kbob/filabilly-humidor/Fan and Surround/Dummy Fan/IMG_1981.jpeg

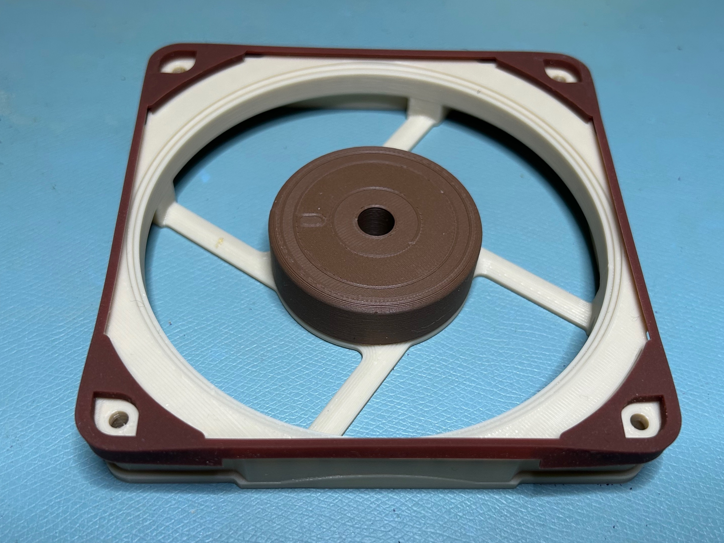
Fan and Surround/Dummy Fan/IMG_1981.jpeg
