kbob/filabilly-humidor/Fan and Surround/Dummy Fan/IMG_1982.jpeg

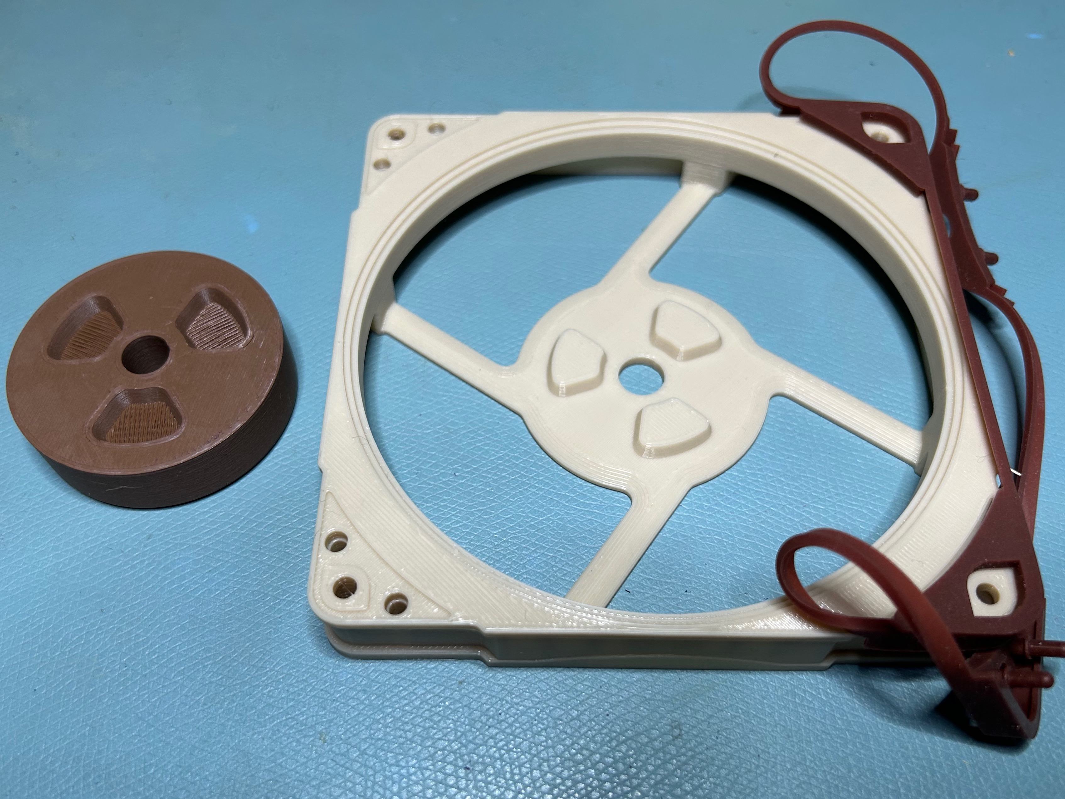
Fan and Surround/Dummy Fan/IMG_1982.jpeg
