kbob/filabilly-humidor/Fan and Surround/Dummy Fan/IMG_1983.jpeg

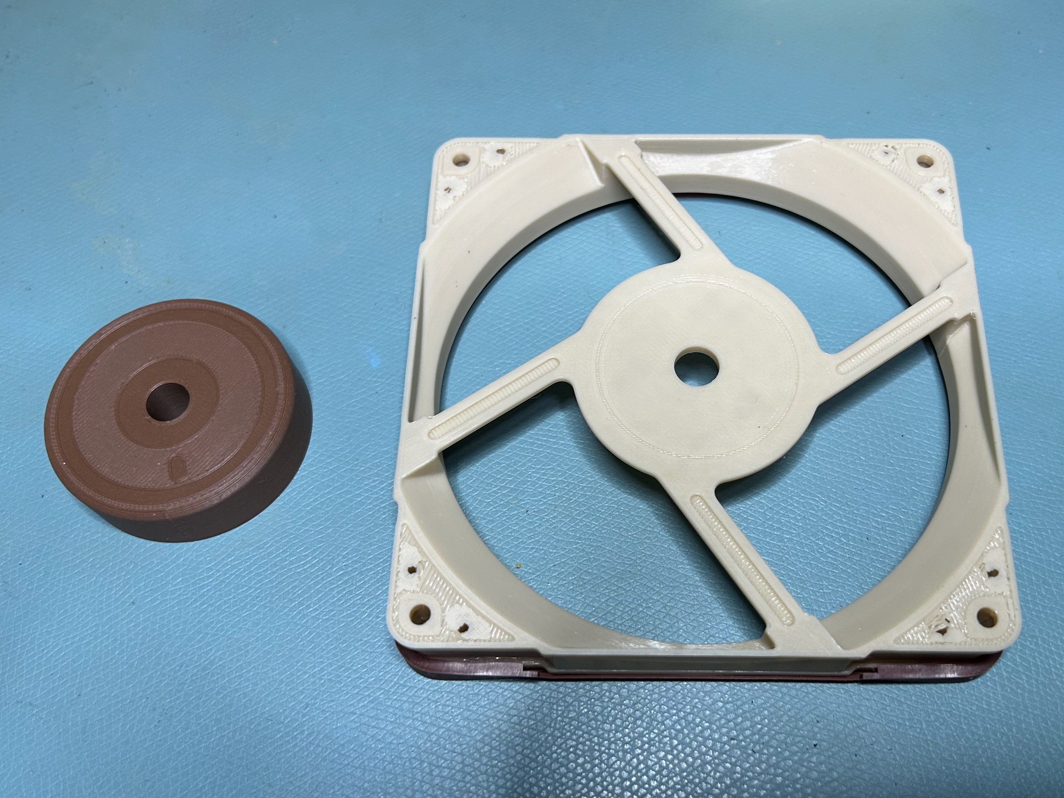
Fan and Surround/Dummy Fan/IMG_1983.jpeg
