kbob/filabilly-humidor/Fan and Surround/Fan Surround/IMG_1965.jpeg

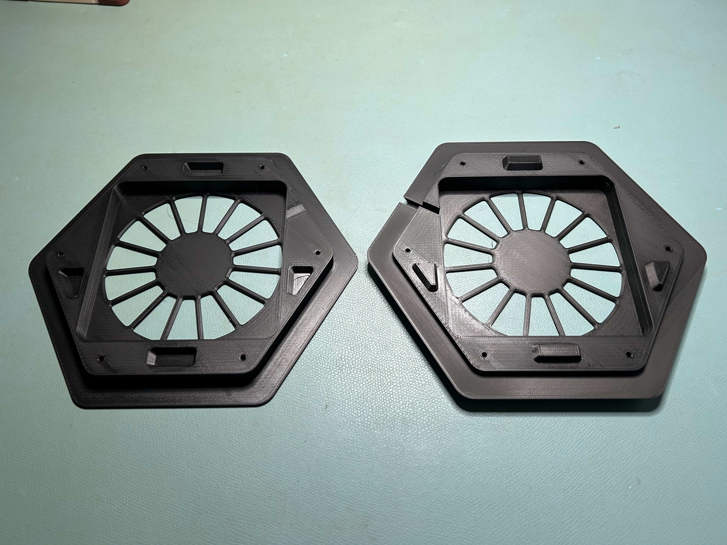
Fan and Surround/Fan Surround/IMG_1965.jpeg
