kbob/filabilly-humidor/Fan and Surround/Fan Surround/IMG_1976.jpeg

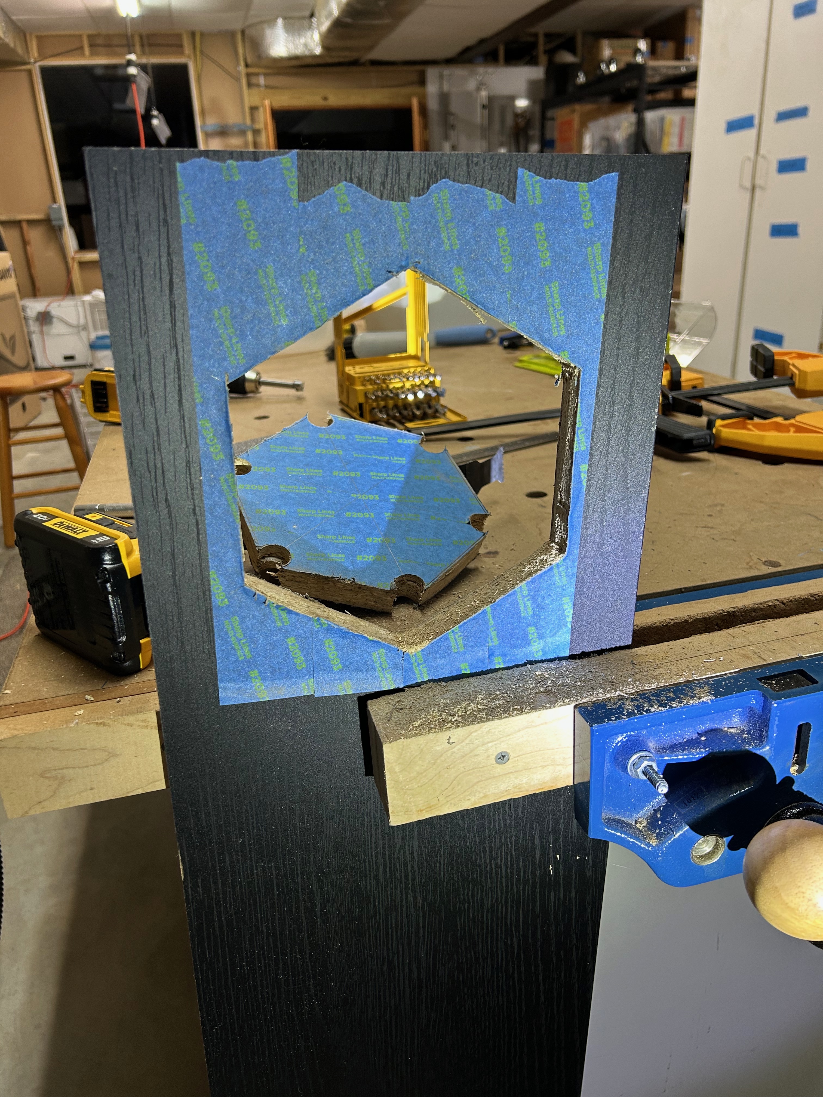
Fan and Surround/Fan Surround/IMG_1976.jpeg
