kbob/filabilly-humidor/Fan and Surround/Fan Surround/IMG_1977.jpeg

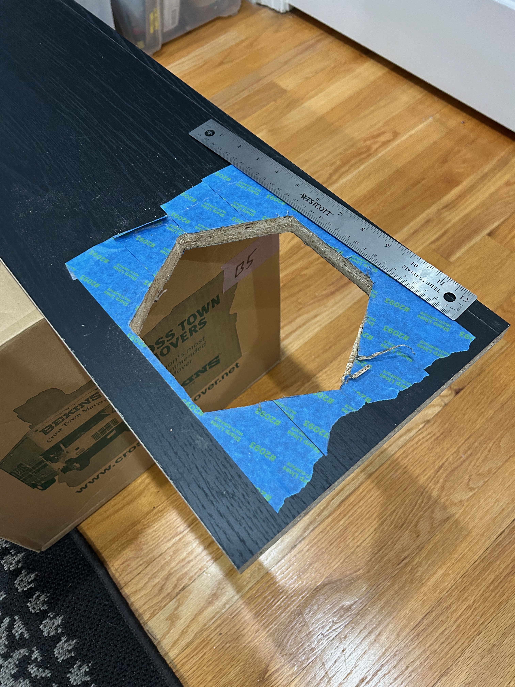
Fan and Surround/Fan Surround/IMG_1977.jpeg
