kbob/filabilly-humidor/Fan and Surround/Fan Surround/IMG_1978.jpeg

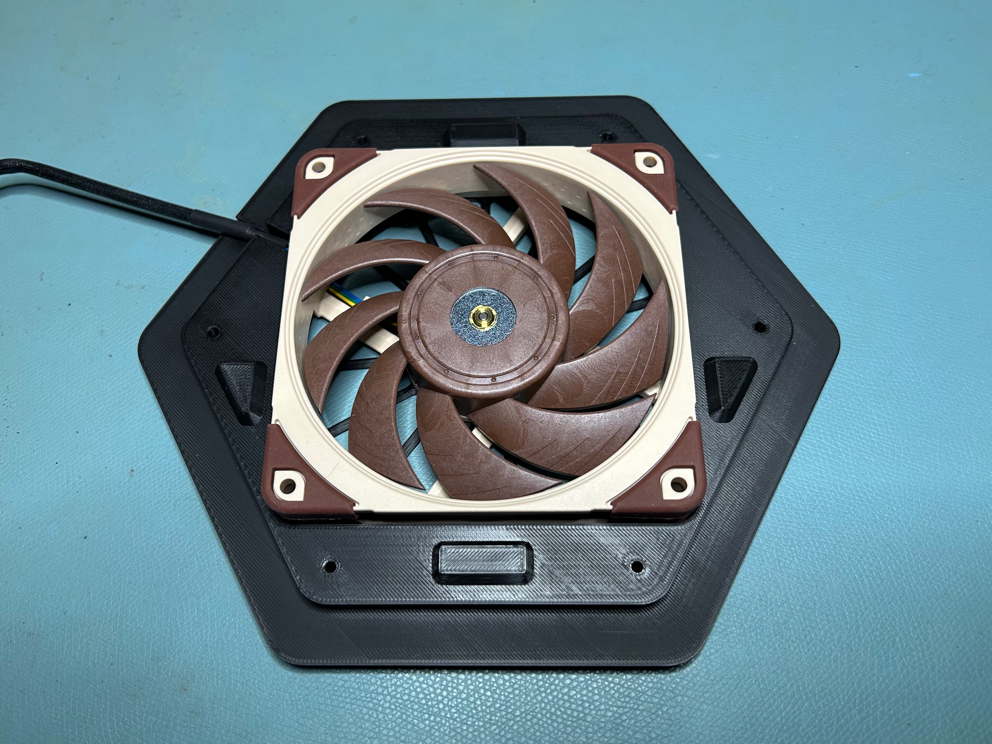
Fan and Surround/Fan Surround/IMG_1978.jpeg
