kbob/filabilly-humidor/Fan and Surround/Fan Surround/IMG_1979.jpeg

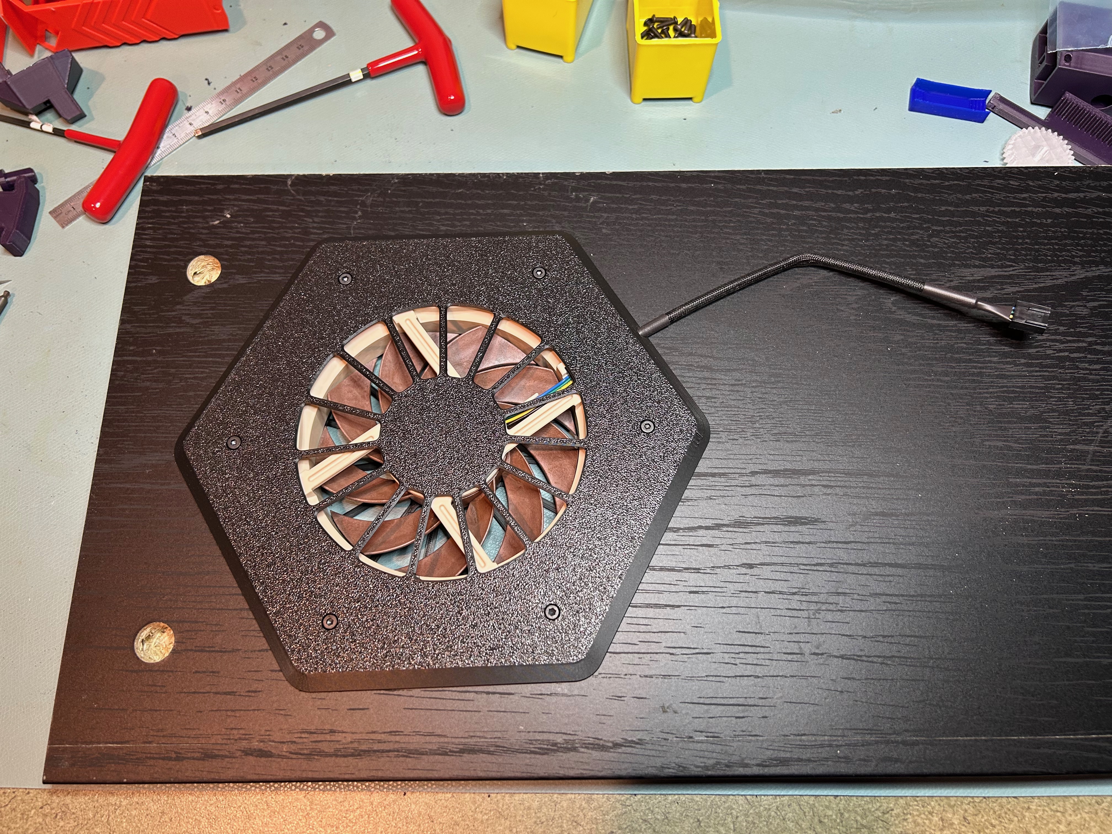
Fan and Surround/Fan Surround/IMG_1979.jpeg
