kbob/filabilly-humidor/Fan and Surround/Fan Surround/IMG_1980.jpeg

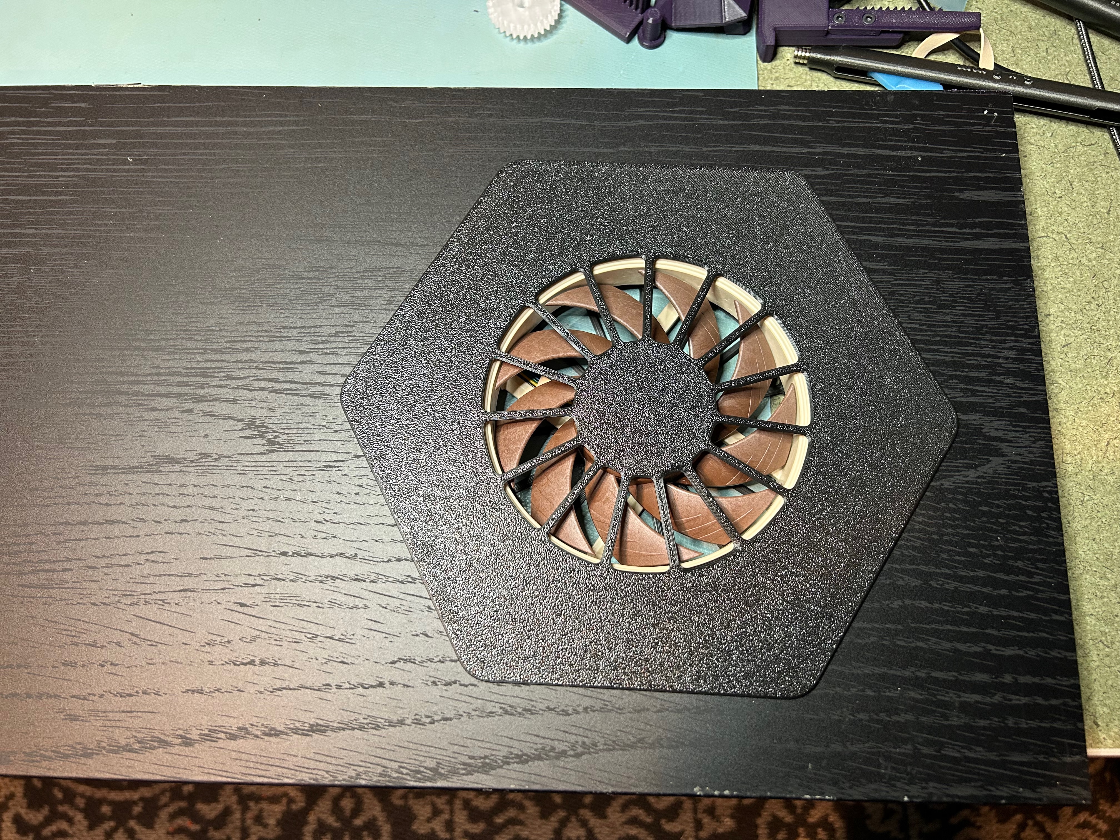
Fan and Surround/Fan Surround/IMG_1980.jpeg
