kbob/filabilly-humidor/Fan and Surround/Fan Surround/IMG_1986.jpeg

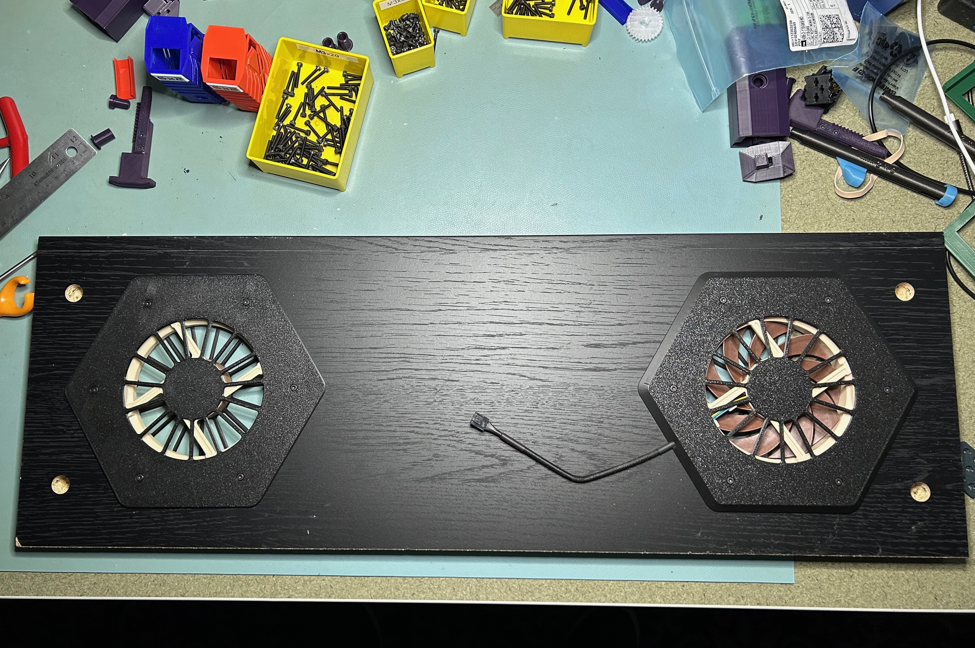
Fan and Surround/Fan Surround/IMG_1986.jpeg
