kbob/filabilly-humidor/Fan and Surround/Fan Surround/IMG_1988.jpeg

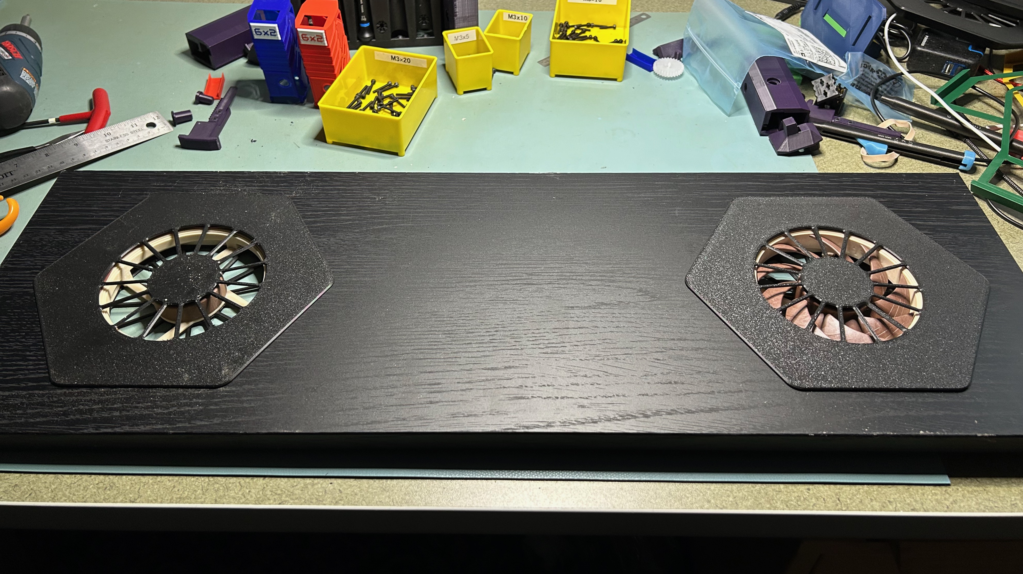
Fan and Surround/Fan Surround/IMG_1988.jpeg
