kbob/filabilly-humidor/Fan and Surround/Fan Surround/Fan Housing Top.stl

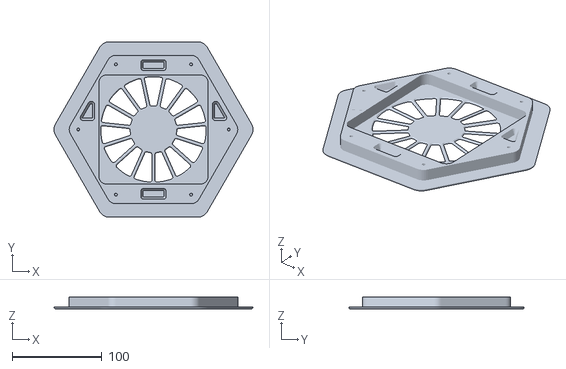
[picture p28: CAD file, 2025-12-27]
Fan and Surround/Fan Surround/Fan Housing Top.stl
221.1 x 194.9 x 13.0
