kbob/filabilly-humidor/Dehumidifier/Printed Parts/STL Files/Housing Left Half.stl

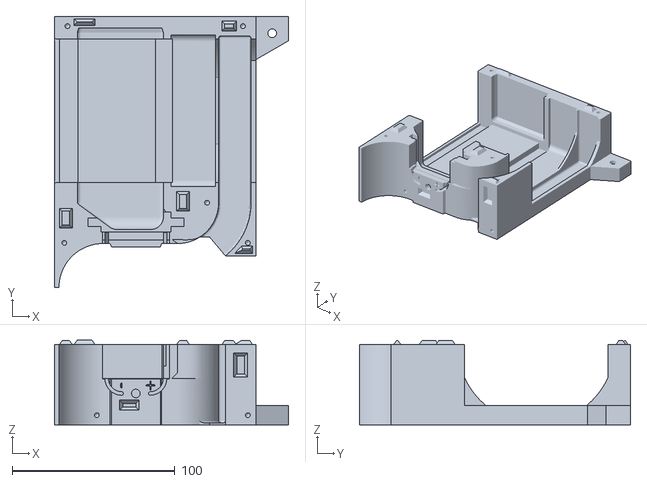
[picture p29: CAD file, 2025-04-28]
Dehumidifier/Printed Parts/STL Files/Housing Left Half.stl
143.8 x 166.7 x 52.2
