kbob/filabilly-humidor/Fan and Surround/Fan Surround/Cutting Guide.stl

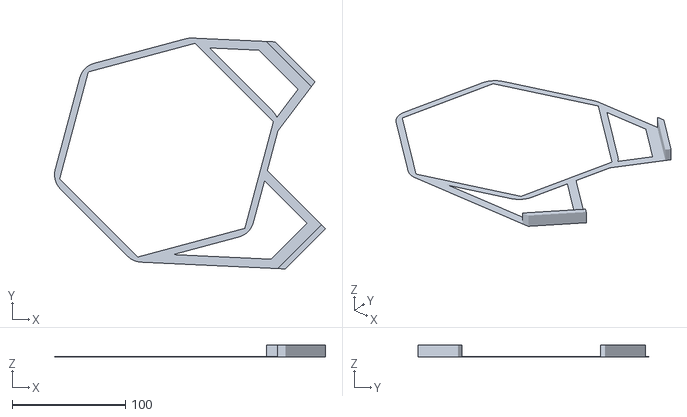
[picture p30: CAD file, 2025-12-27]
Fan and Surround/Fan Surround/Cutting Guide.stl
238.9 x 203.6 x 10.6
