kbob/filabilly-humidor/Dehumidifier/Printed Parts/STL Files/Bottom Vent Slider.stl

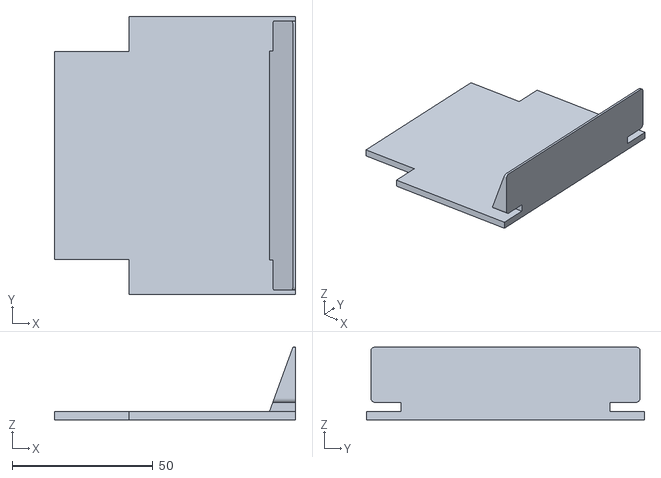
[picture p31: CAD file, 2025-04-28]
Dehumidifier/Printed Parts/STL Files/Bottom Vent Slider.stl
85.7 x 98.7 x 25.8
