kbob/filabilly-humidor/Dehumidifier/Printed Parts/STL Files/DHT22 Standoff.stl

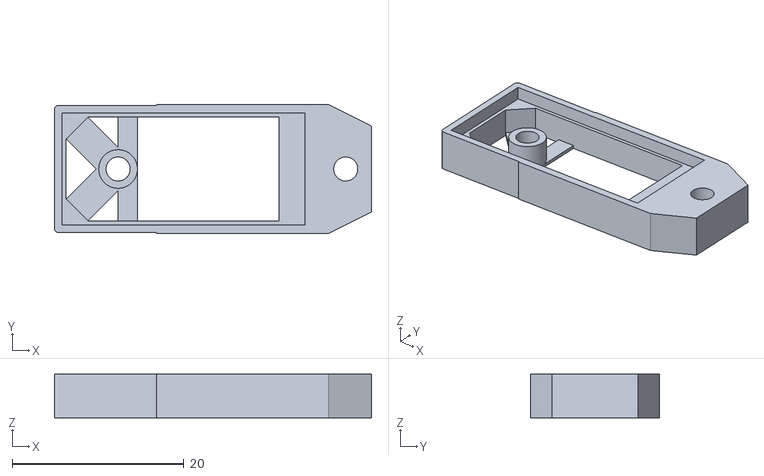
[picture p32: CAD file, 2025-04-28]
Dehumidifier/Printed Parts/STL Files/DHT22 Standoff.stl
36.9 x 15.0 x 5.10
