kbob/filabilly-humidor/Dehumidifier/Printed Parts/STL Files/Housing Right Half.stl

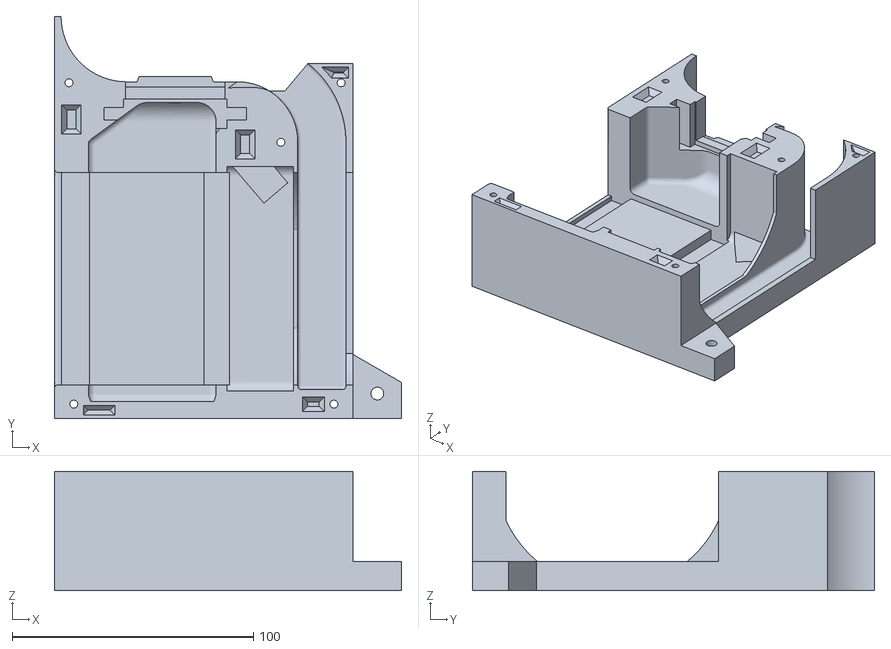
[picture p33: CAD file, 2025-04-28]
Dehumidifier/Printed Parts/STL Files/Housing Right Half.stl
143.8 x 166.7 x 49.3
