kbob/filabilly-humidor/Dehumidifier/Printed Parts/STL Files/Electronics Cover.stl

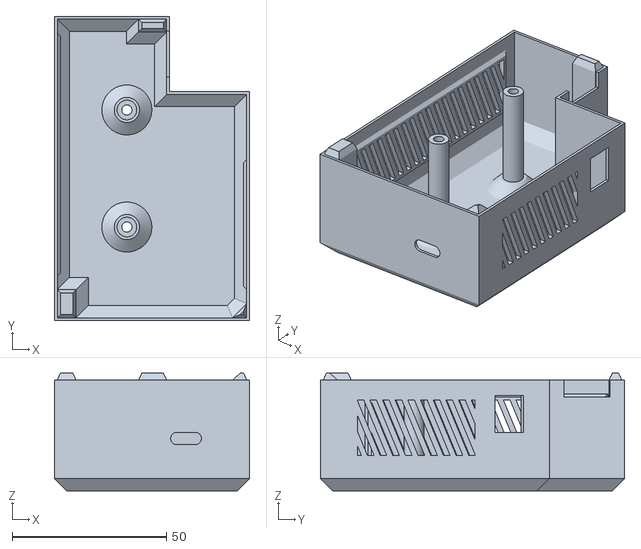
[picture p34: CAD file, 2025-04-28]
Dehumidifier/Printed Parts/STL Files/Electronics Cover.stl
63.3 x 98.7 x 38.2
